mohankumargupta/brian-petrol-signs/B.png

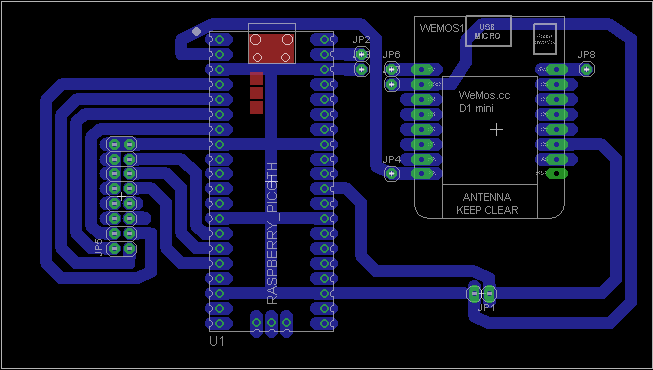
B.png
