mohankumargupta/brian-petrol-signs/C.png

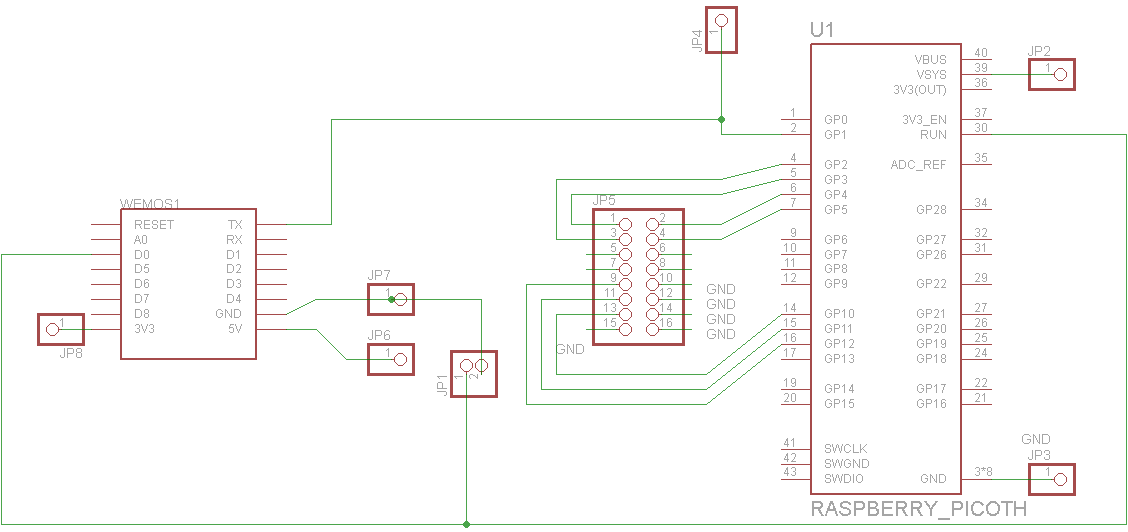
C.png
