mohankumargupta/brian-petrol-signs/D.png

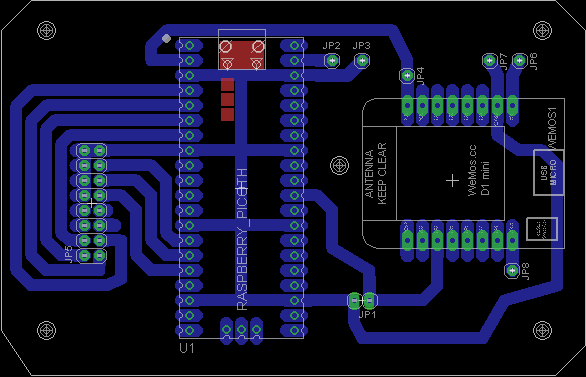
D.png
