mohankumargupta/brian-petrol-signs/eagle/brianPCB-bottom2.png

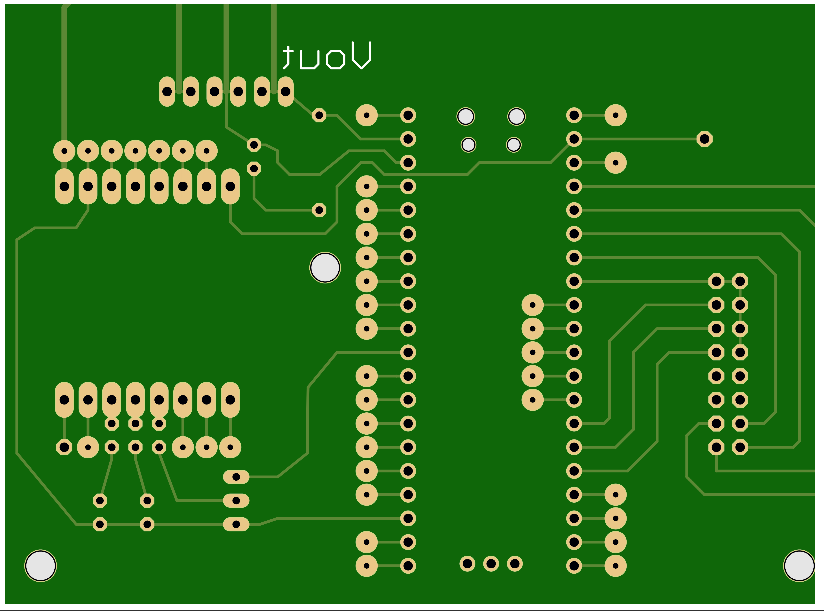
eagle/brianPCB-bottom2.png
