mohankumargupta/brian-petrol-signs/eagle/brianPCB-bottom.png

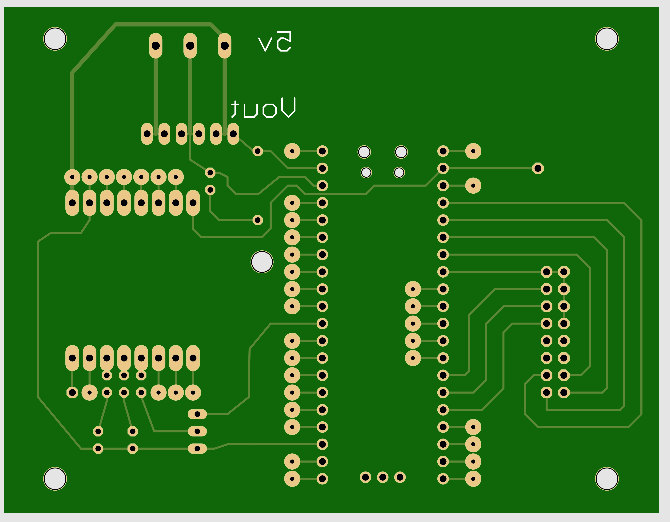
eagle/brianPCB-bottom.png
