mohankumargupta/brian-petrol-signs/eagle/brianPCB-top2.png

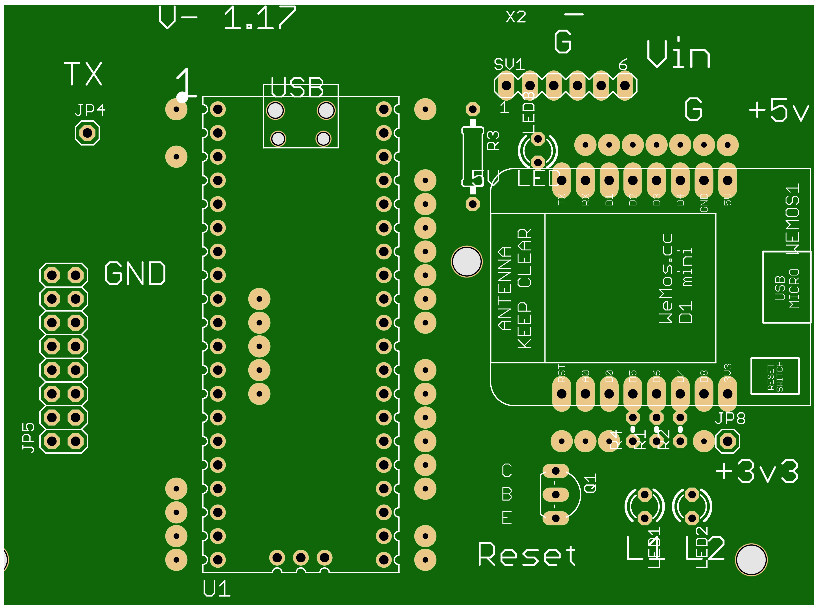
eagle/brianPCB-top2.png
