mohankumargupta/brian-petrol-signs/eagle/brianPCB-top.png

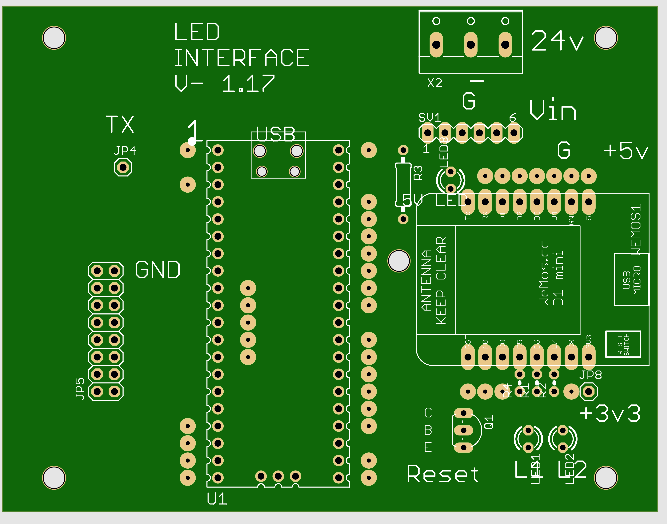
eagle/brianPCB-top.png
