mohankumargupta/brian-petrol-signs/eagle/Brians board 5.jpg

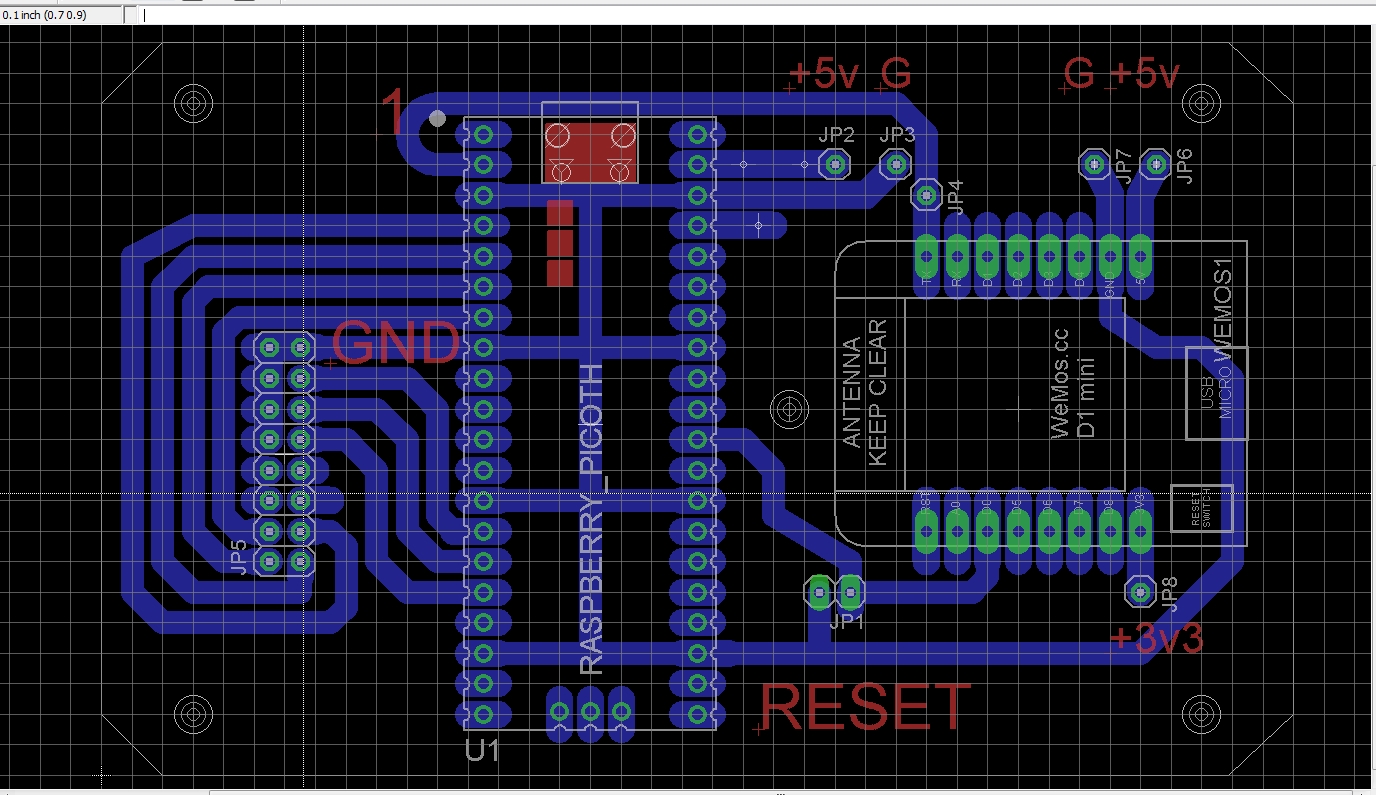
eagle/Brians board 5.jpg
