mohankumargupta/brian-petrol-signs/eagle/Brians board 7.jpg

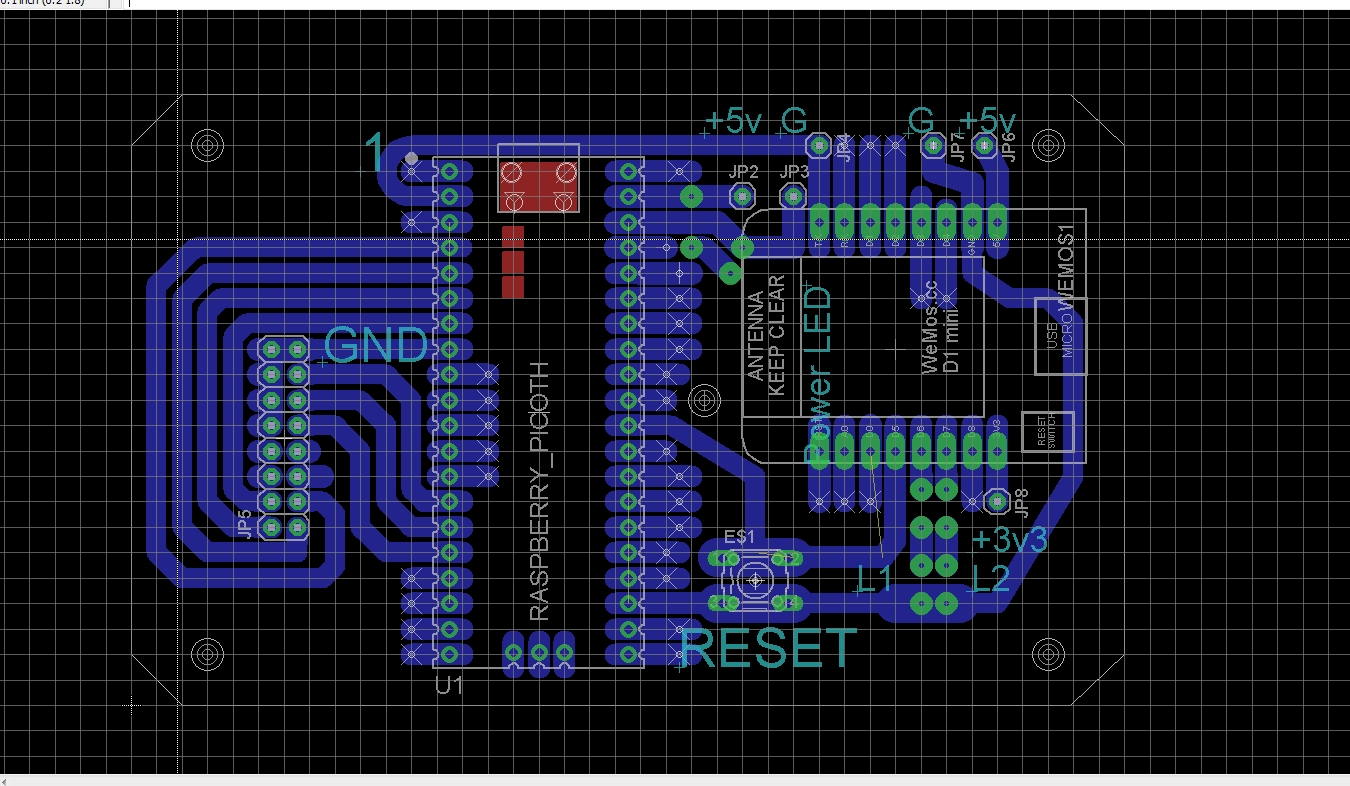
eagle/Brians board 7.jpg
