mohankumargupta/brian-petrol-signs/eagle/Brians LED Brd6..jpg

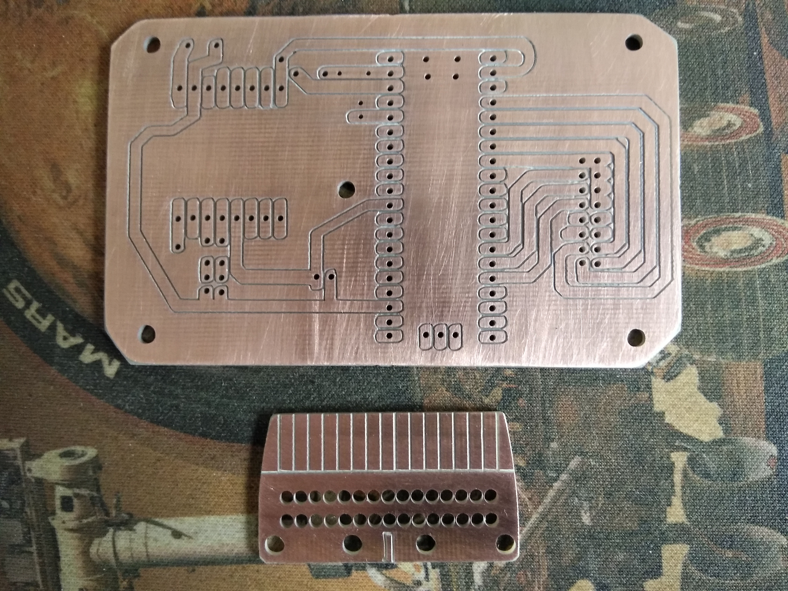
eagle/Brians LED Brd6..jpg
