mohankumargupta/brian-petrol-signs/eagle/Brians LED Brd6Top..jpg

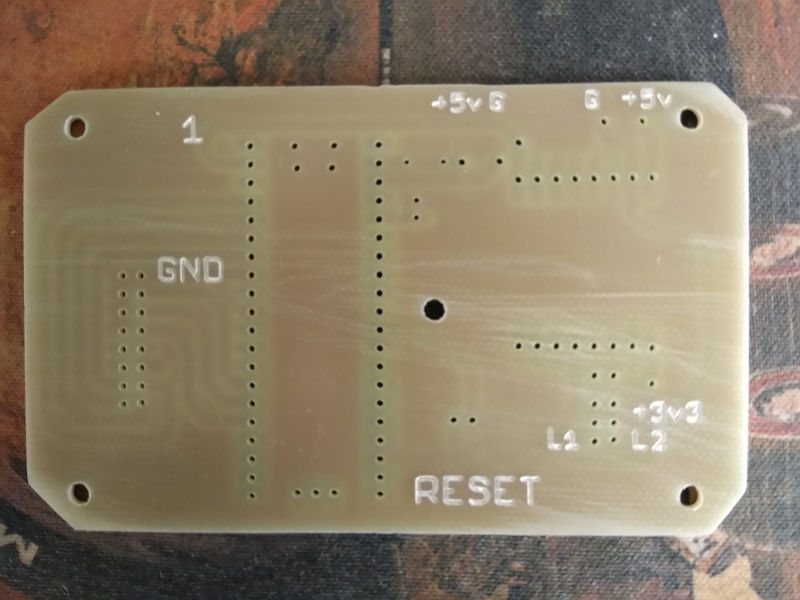
eagle/Brians LED Brd6Top..jpg
