mohankumargupta/brian-petrol-signs/eagle/jlcpcb-12-bottom.png

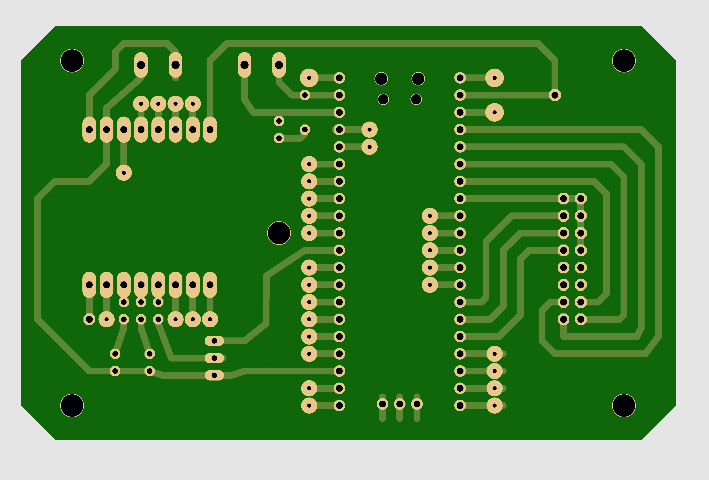
eagle/jlcpcb-12-bottom.png
