mohankumargupta/brian-petrol-signs/eagle/jlcpcb-12-top.png

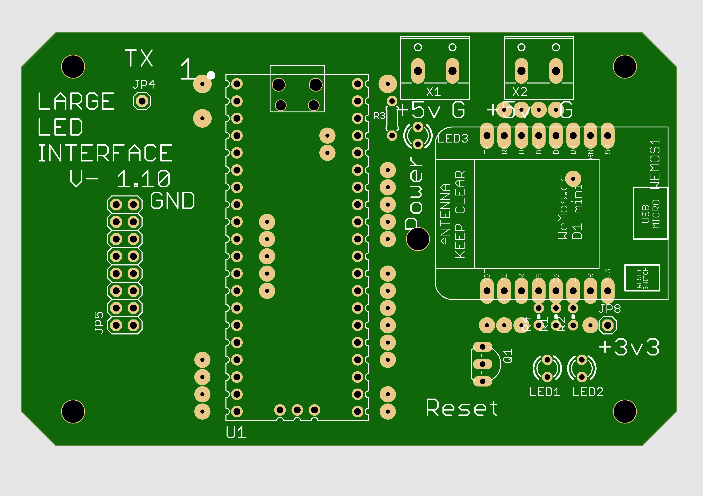
eagle/jlcpcb-12-top.png
