mohankumargupta/brian-petrol-signs/eagle/Pico Image 3.jpg

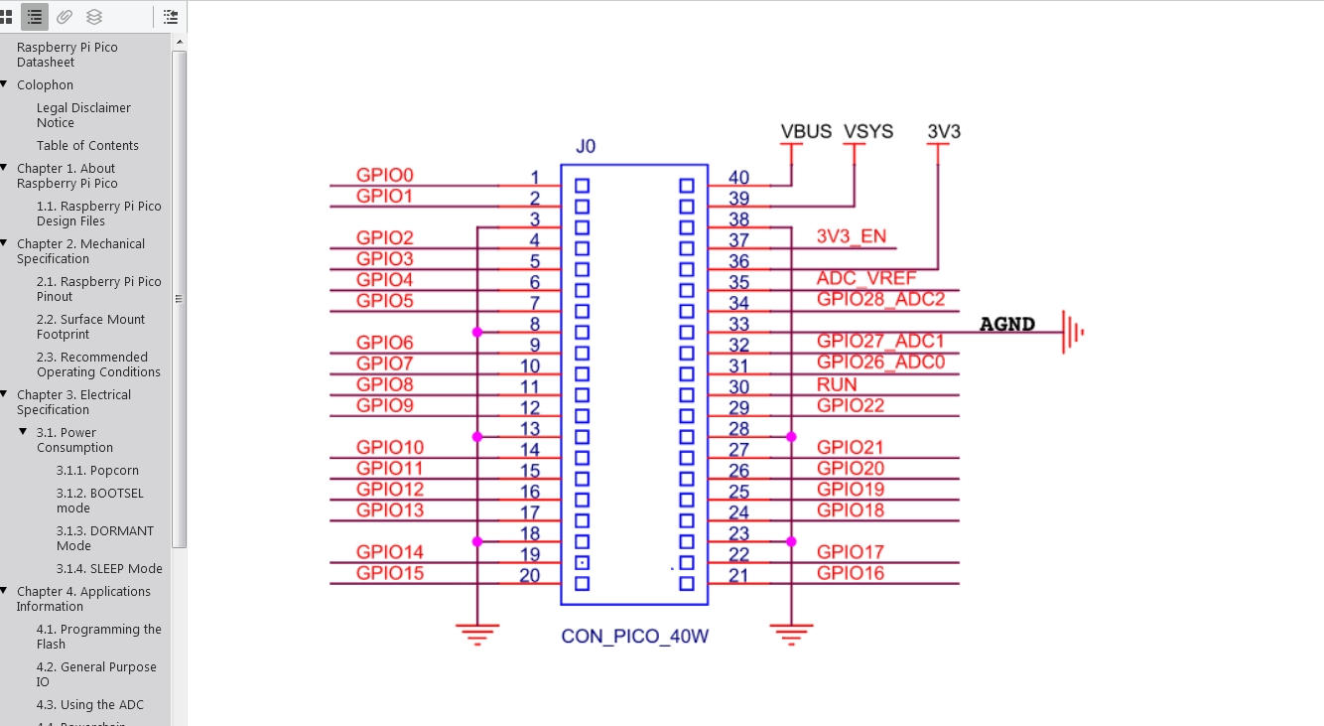
eagle/Pico Image 3.jpg
