mohankumargupta/brian-petrol-signs/esp8266-lolinv3.jpg

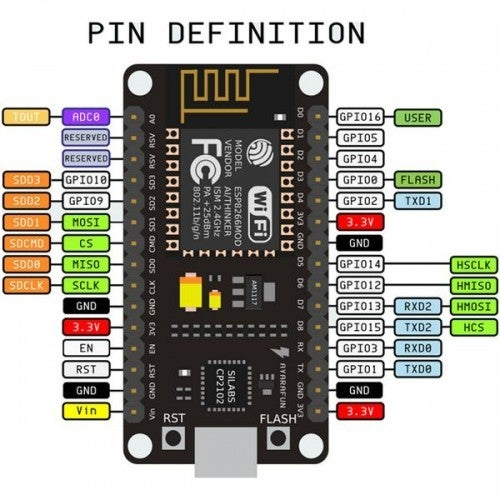
esp8266-lolinv3.jpg
