mohankumargupta/brian-petrol-signs/HD-HUB75-08-HUB08-transfer-to-HUB75-port-75-08-Converter-adapter-LED-sign-conversion-card.jpg_Q90.jpg_.jpg

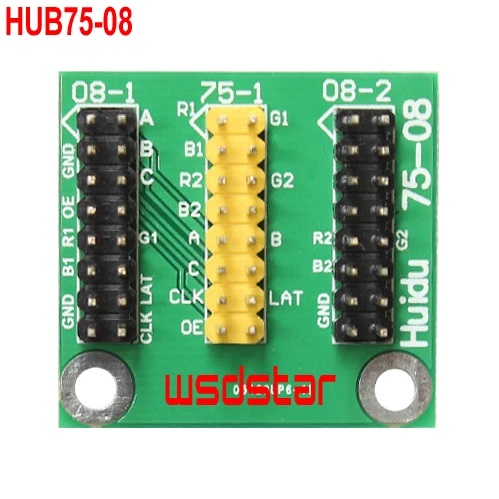
HD-HUB75-08-HUB08-transfer-to-HUB75-port-75-08-Converter-adapter-LED-sign-conversion-card.jpg_Q90.jpg_.jpg
