mohankumargupta/brian-petrol-signs/images/20210626_175642.jpg

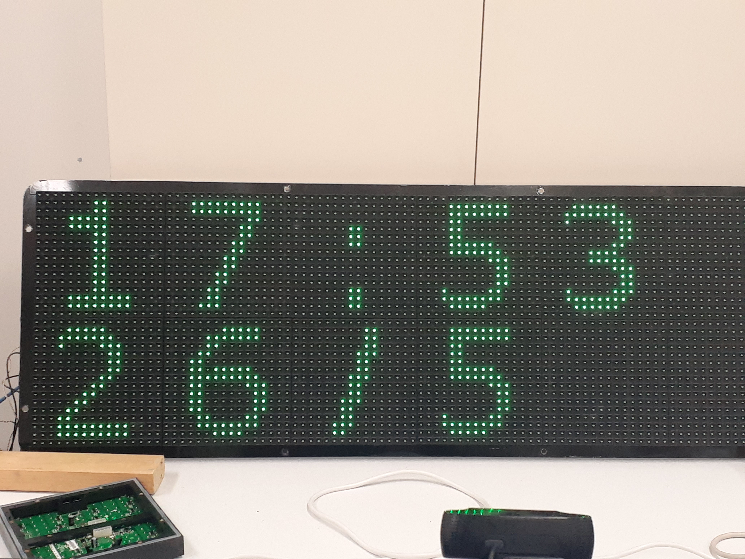
images/20210626_175642.jpg
