mohankumargupta/brian-petrol-signs/images/20210626_175735.jpg

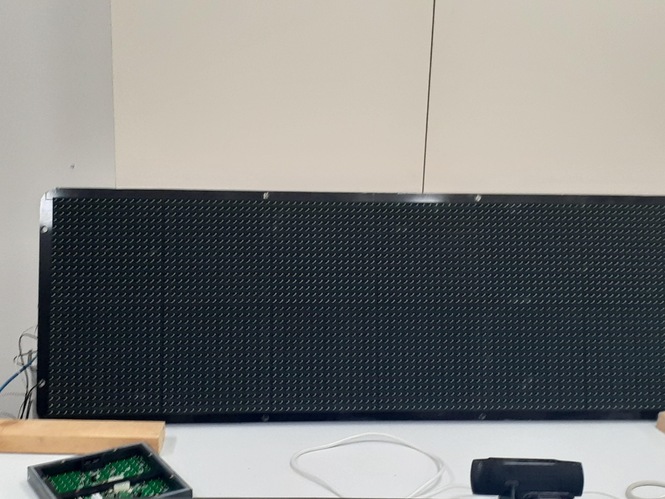
images/20210626_175735.jpg
