mohankumargupta/brian-petrol-signs/images/20210626_175953.jpg

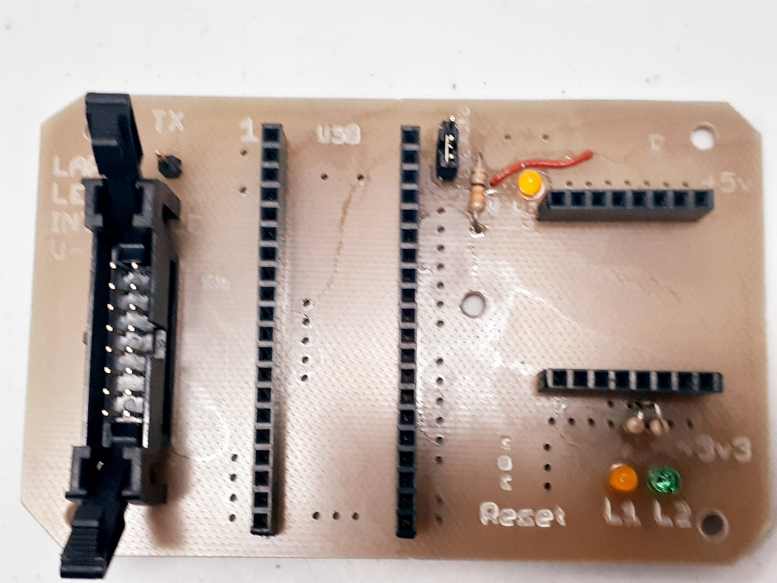
images/20210626_175953.jpg
