mohankumargupta/brian-petrol-signs/images/buckconverter.png

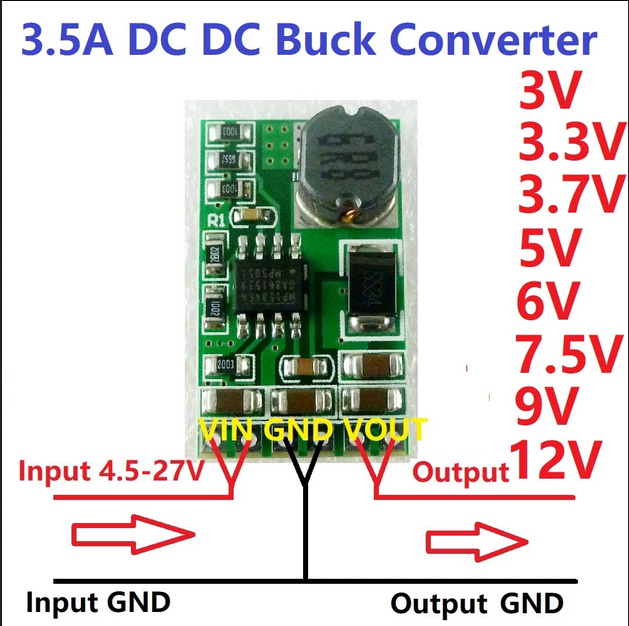
images/buckconverter.png
