mohankumargupta/brian-petrol-signs/images/esphomeflasher.jpg

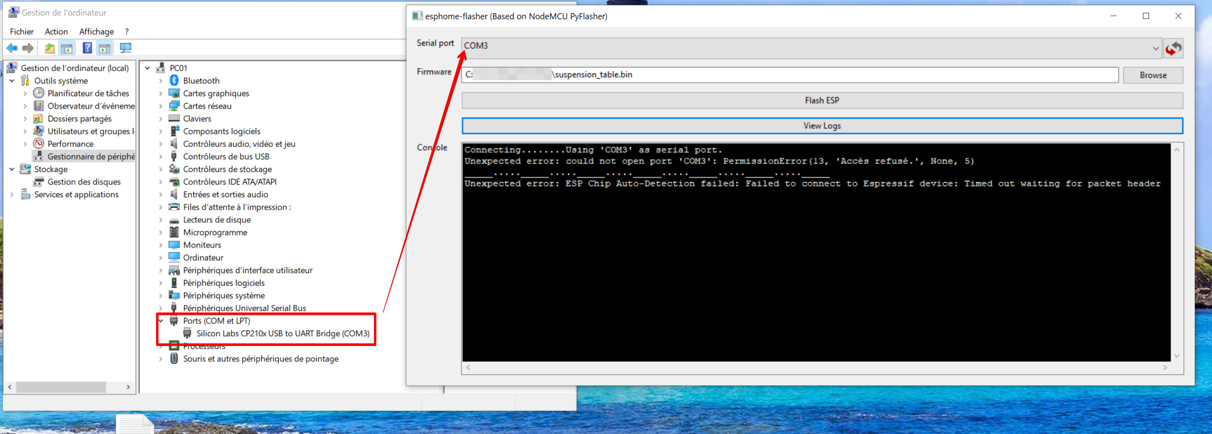
images/esphomeflasher.jpg
