mohankumargupta/brian-petrol-signs/IMG_1820-redacted.jpg

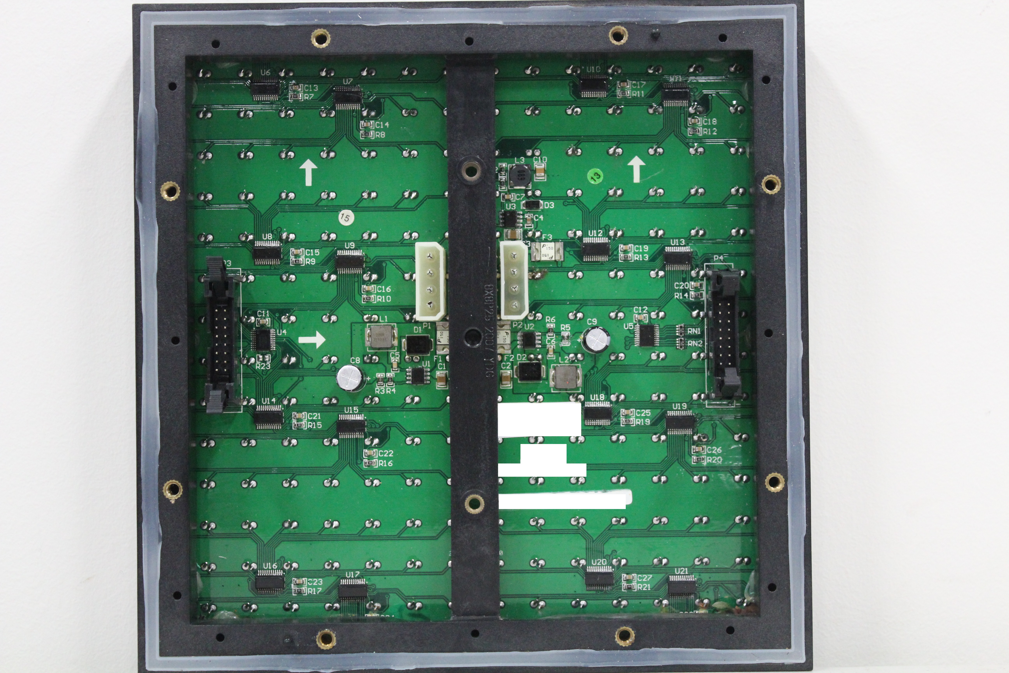
IMG_1820-redacted.jpg
