mohankumargupta/brian-petrol-signs/MBI5039-timing.png

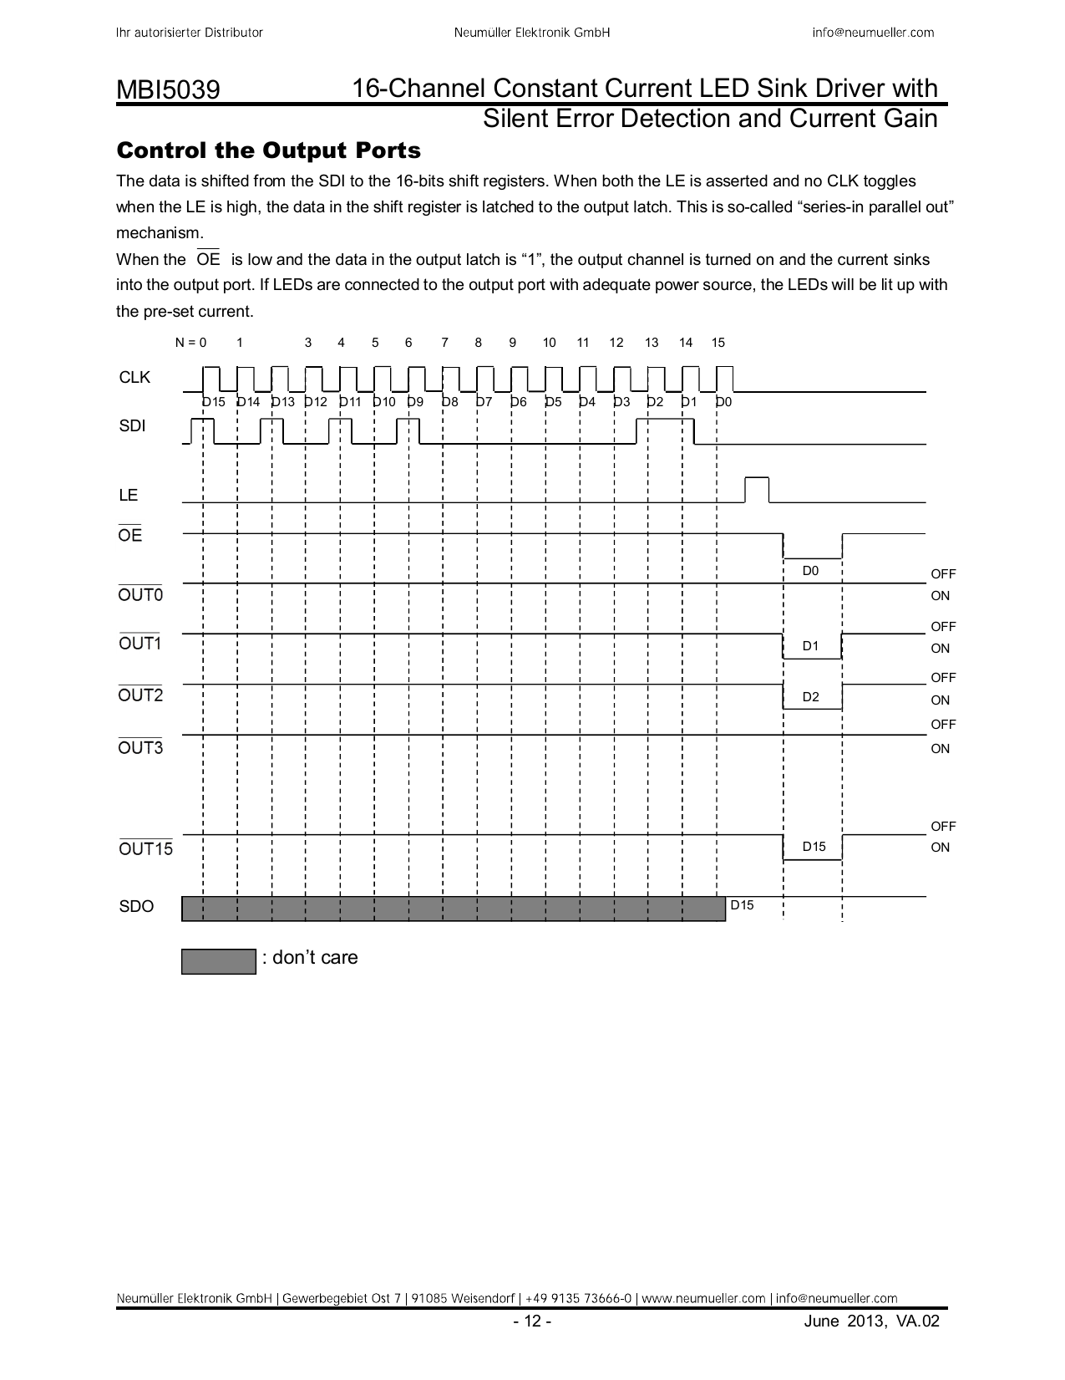
MBI5039-timing.png
