mohankumargupta/brian-petrol-signs/microcontrollers/sch_d1_mini_v3.0.0.png

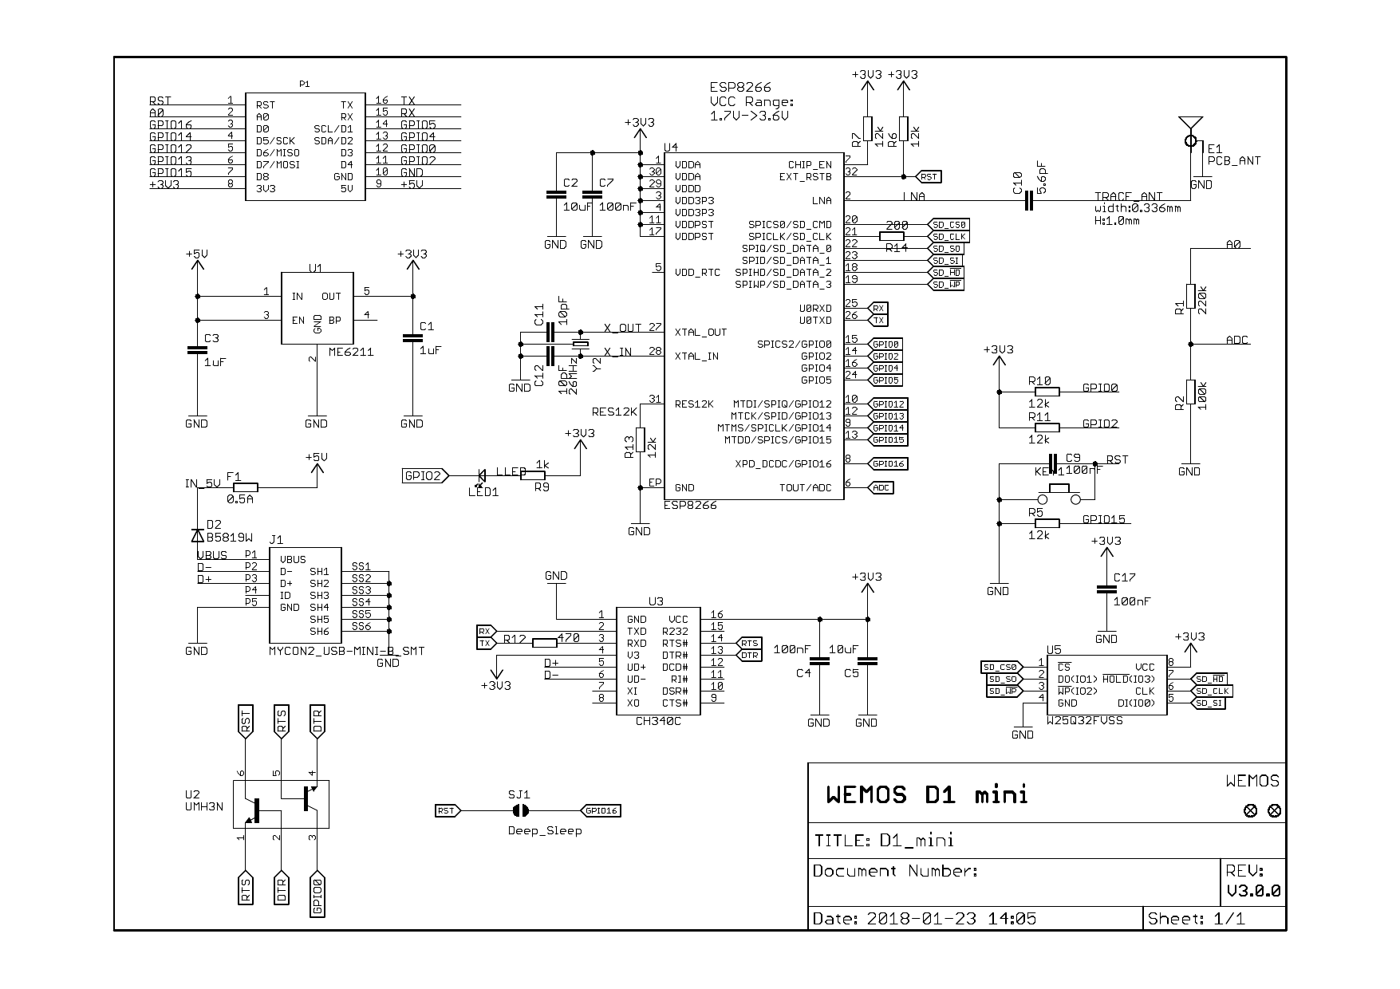
microcontrollers/sch_d1_mini_v3.0.0.png
