mohankumargupta/brian-petrol-signs/pico-powertrain-schottky.png

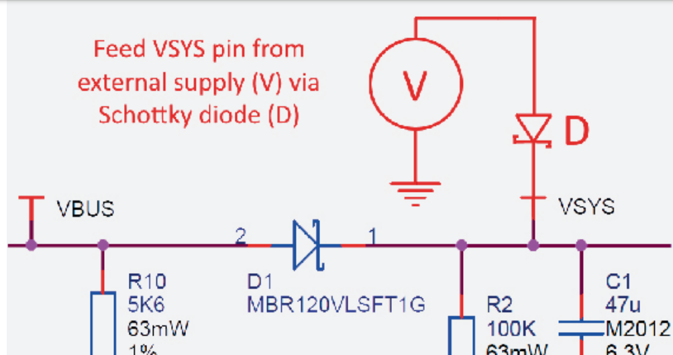
pico-powertrain-schottky.png
