mohankumargupta/brian-petrol-signs/pico-powertrain.png

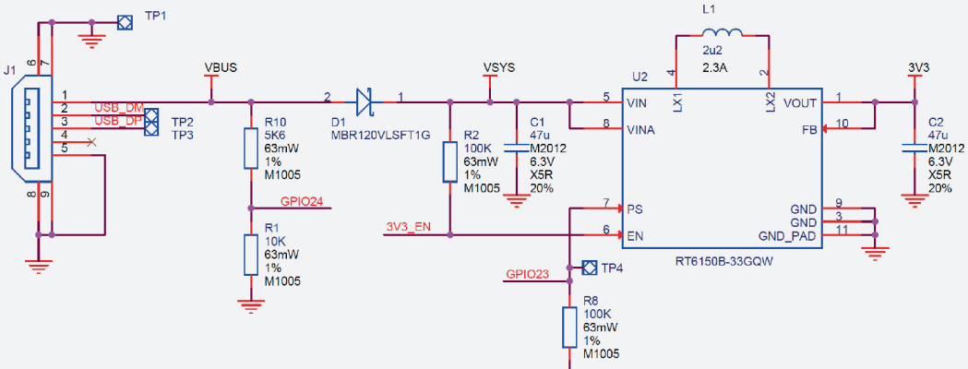
pico-powertrain.png
