mohankumargupta/brian-petrol-signs/eagle/Brians test board 1.12a-bottomPCB-mohan.png

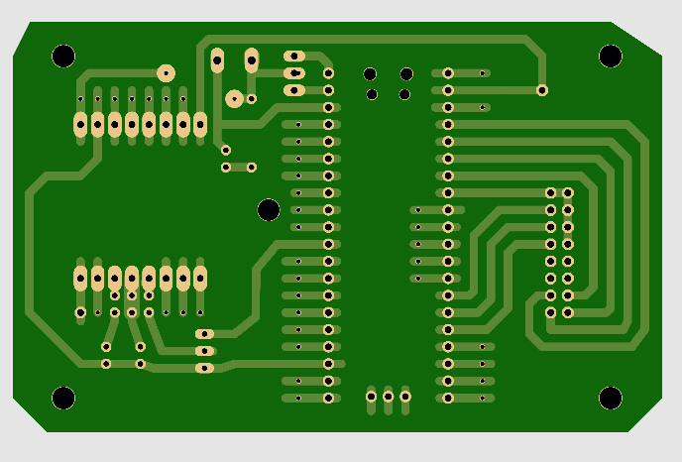
eagle/Brians test board 1.12a-bottomPCB-mohan.png
