mohankumargupta/brian-petrol-signs/eagle/Brians test board 12.png

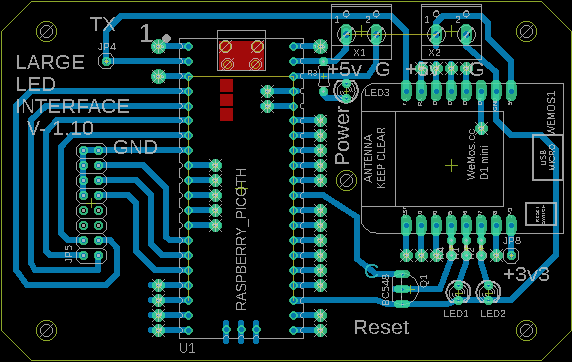
eagle/Brians test board 12.png
