mohankumargupta/brian-petrol-signs/eagle/Brians test board 16-top.png

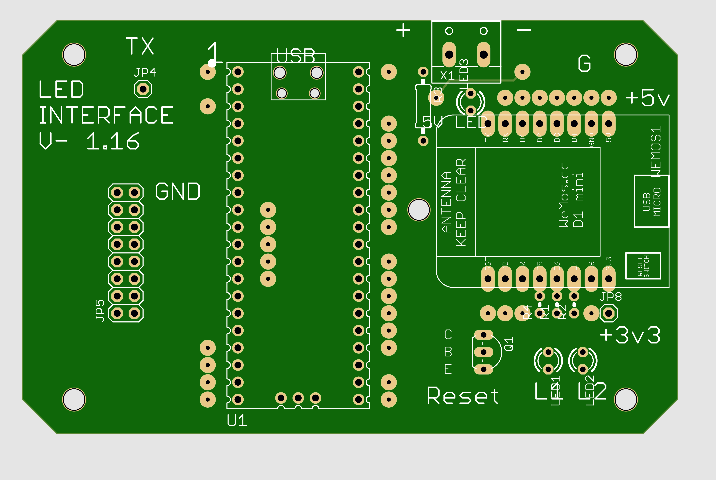
eagle/Brians test board 16-top.png
