mohankumargupta/brian-petrol-signs/eagle/Brians test board 17-board.png

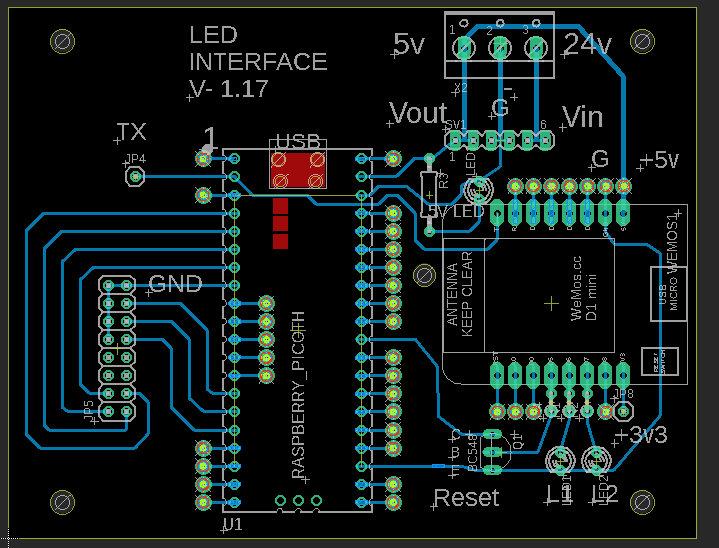
eagle/Brians test board 17-board.png
