mohankumargupta/brian-petrol-signs/eagle/Brians test board 17-schematic.png

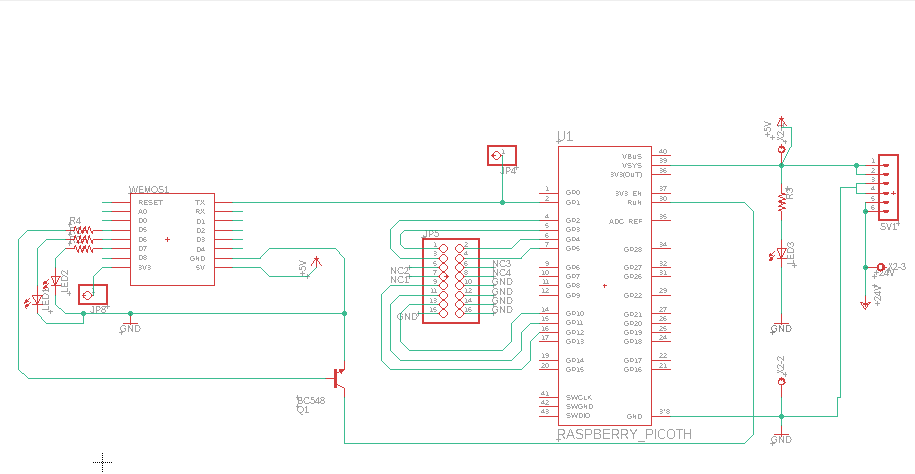
eagle/Brians test board 17-schematic.png
