mohankumargupta/brian-petrol-signs/code/pico/demo-singlepanel/customglcdfonts.h

#pragma once

#if defined(ARDUINO_ARCH_RP2040)
#define PROGMEM
#endif

const static uint8_t ArialFont16x16[] PROGMEM = {
    0x0, 0x0, // size
    0x10, // width
    0x10, // height
    0x20, // first char
    0x60, // char count  
  
0x00, 0x00, 0x00, 0x00, 0x00, 0x00, 0x00, 0x00, 0x00, 0x00, 0x00, 0x00, 0x00, 0x00, 0x00, 0x00, 0x00, 0x00, 0x00, 0x00, 0x00, 0x00, 0x00, 0x00, 0x00, 0x00, 0x00, 0x00, 0x00, 0x00, 0x00, 0x00,  // Code for char  
0x00, 0x00, 0x00, 0x00, 0xFE, 0x17, 0x00, 0x00, 0x00, 0x00, 0x00, 0x00, 0x00, 0x00, 0x00, 0x00, 0x00, 0x00, 0x00, 0x00, 0x00, 0x00, 0x00, 0x00, 0x00, 0x00, 0x00, 0x00, 0x00, 0x00, 0x00, 0x00,  // Code for char !
0x00, 0x00, 0x1E, 0x00, 0x00, 0x00, 0x00, 0x00, 0x1E, 0x00, 0x00, 0x00, 0x00, 0x00, 0x00, 0x00, 0x00, 0x00, 0x00, 0x00, 0x00, 0x00, 0x00, 0x00, 0x00, 0x00, 0x00, 0x00, 0x00, 0x00, 0x00, 0x00,  // Code for char "
0x20, 0x02, 0x20, 0x1E, 0xF0, 0x03, 0x2E, 0x02, 0x20, 0x02, 0x20, 0x1E, 0xF0, 0x03, 0x2E, 0x02, 0x20, 0x02, 0x00, 0x00, 0x00, 0x00, 0x00, 0x00, 0x00, 0x00, 0x00, 0x00, 0x00, 0x00, 0x00, 0x00,  // Code for char #
0x00, 0x00, 0x38, 0x04, 0x44, 0x08, 0x42, 0x10, 0xFF, 0x3F, 0x82, 0x10, 0x82, 0x08, 0x0C, 0x07, 0x00, 0x00, 0x00, 0x00, 0x00, 0x00, 0x00, 0x00, 0x00, 0x00, 0x00, 0x00, 0x00, 0x00, 0x00, 0x00,  // Code for char $
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
0xFE, 0x0F, 0x02, 0x08, 0x02, 0x08, 0xFE, 0x0F, 0x00, 0x00, 0x00, 0x00, 0x00, 0x00, 0x00, 0x00, 0x00, 0x00, 0x00, 0x00, 0x00, 0x00, 0x00, 0x00, 0x00, 0x00, 0x00, 0x00, 0x00, 0x00, 0x00, 0x00   // Code for char 
};
