mohankumargupta/brian-petrol-signs/code/pico/demo-multipanel/test11command.h

#pragma once

#include "command.h"

class Test11Command : public Command
{
  private:
    unsigned long timeStart = 0UL;
    DMD3 *scrollingCanvas;
    int currentScrollX = 0;
    int scrollTextSize = 0;
    int counter = 0;
    bool scrollingMode = false;
  
  public:
    Test11Command() {
      scrollingCanvas = new DMD3(40,1);
      scrollingCanvas->setFont(VerdanaFont16x16);
      scrollingCanvas->clear();
      scrollingCanvas->drawText(96,0,"AND A HAPPY NEW YEAR");      
      scrollTextSize = 16 * sizeof("AND A HAPPY NEW YEAR") + 106;      
    }

    void print(uint8_t *data) 
{
  Serial.print(" 0x");
  Serial.print(*data >> 4, HEX);
  Serial.print(*data & 0x0F, HEX); 
}

    void printScrollingCanvas(DMD3 *canvas)
    {
      if (DEBUG)
      {
        char buf[100];
        for (int i=0; i < 32; i++) 
        {
          scrollingCanvas->debugPixelLine(i, buf);
          Serial.println(buf);    
        }
      } 
    }
  
    void execute(DMD3 *canvas)  override {
      if ( millis() - timeStart > 70) {        
        clearSerialMonitor();
        canvas->clear();       

        switch(scrollingMode) {
          case false:
            canvas->drawText(8,0,"MERRY");
            canvas->drawText(9,16, "XMAS!");
            if (counter++ > 50) {
              counter = 0;
              scrollingMode = true;             
            }
            break;
          case true:
            scrollingCanvas->copy(currentScrollX,0,96,16,canvas,0,16);
            canvas->drawText(0,0, " | | |");
            if (counter++ > 350) {
             counter = 0;
             currentScrollX = 0;
             scrollingMode = false;  
            }
            break;
        }
         
        printCanvas(canvas);
        canvas->update();
        if (currentScrollX++ > scrollTextSize) {
          currentScrollX = 0;
        }
        timeStart = millis();
        
      }
    }
};
